crono2250/CL-Feeder_MountingPlate_and_Control/firmware/OpenPnP2_Settings/Actuator_Settings_PostPick.png

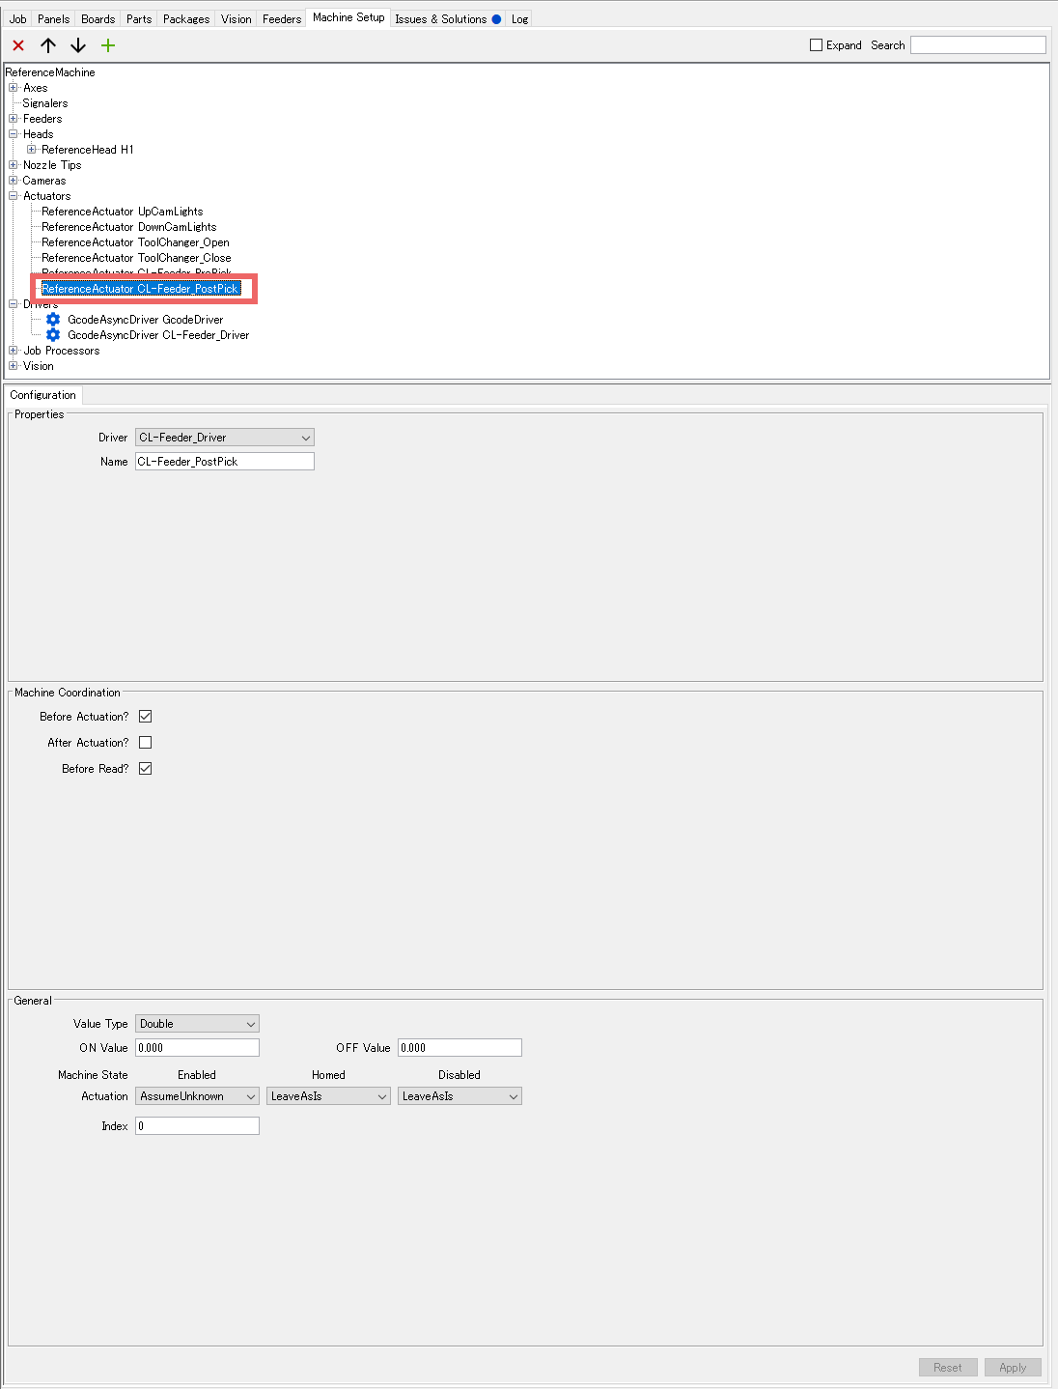
firmware/OpenPnP2_Settings/Actuator_Settings_PostPick.png
