crono2250/CL-Feeder_MountingPlate_and_Control/firmware/OpenPnP2_Settings/GCodeAsyncDriver_Actuator_List.png

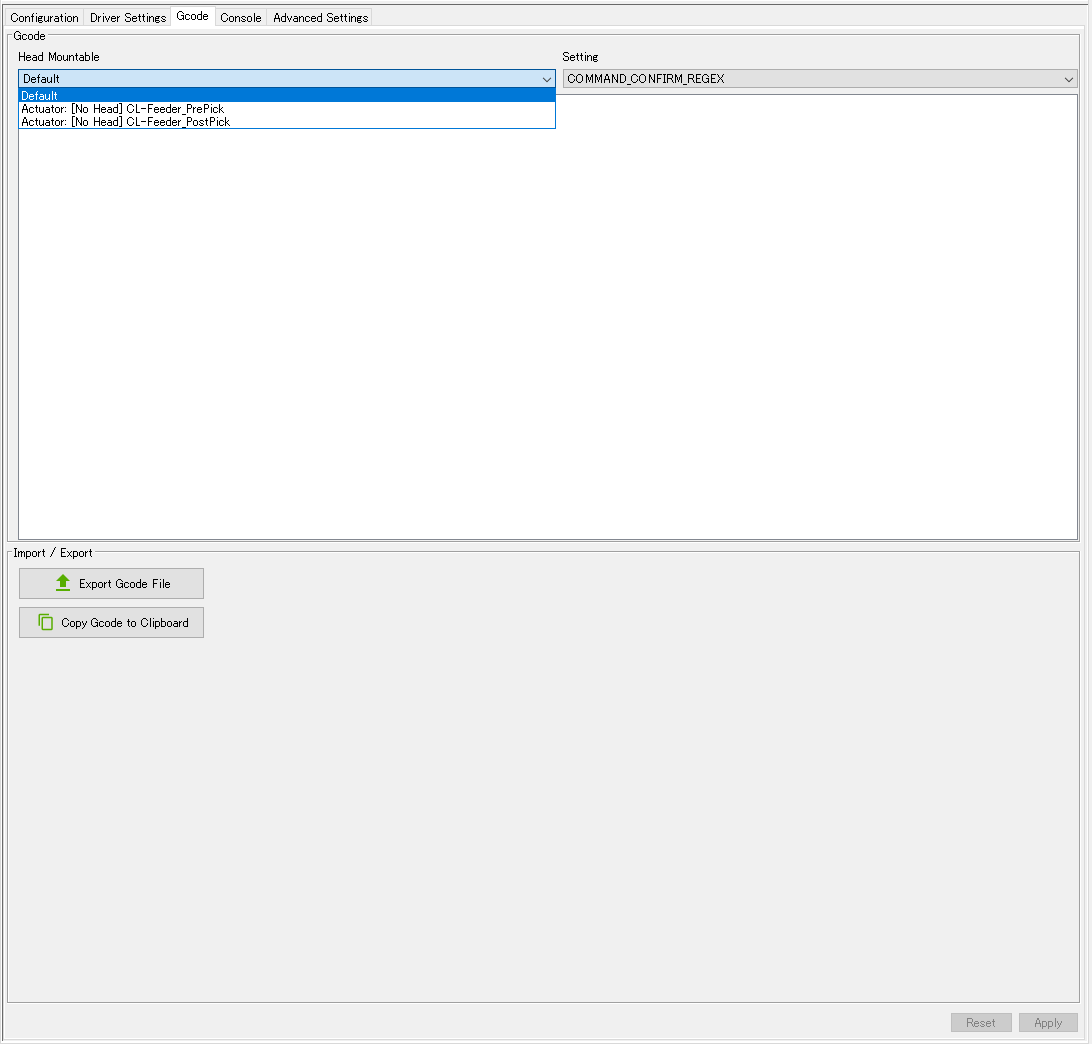
firmware/OpenPnP2_Settings/GCodeAsyncDriver_Actuator_List.png
