crono2250/CL-Feeder_MountingPlate_and_Control/mechanical/img/BuildExample.jpg

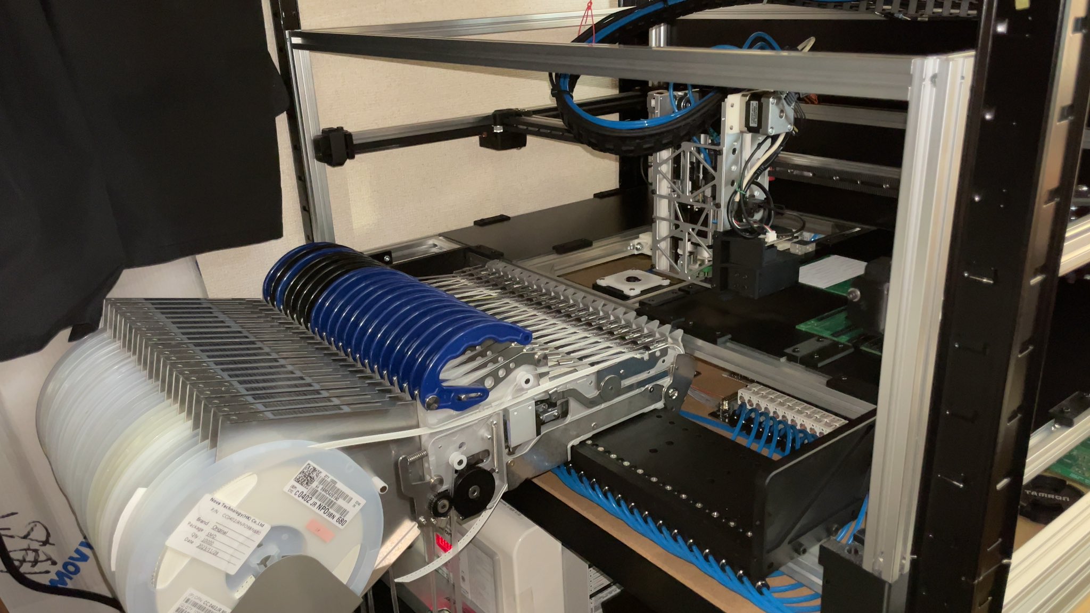
mechanical/img/BuildExample.jpg
