crono2250/CL-Feeder_MountingPlate_and_Control/mechanical/img/BuildExample_CAD.png

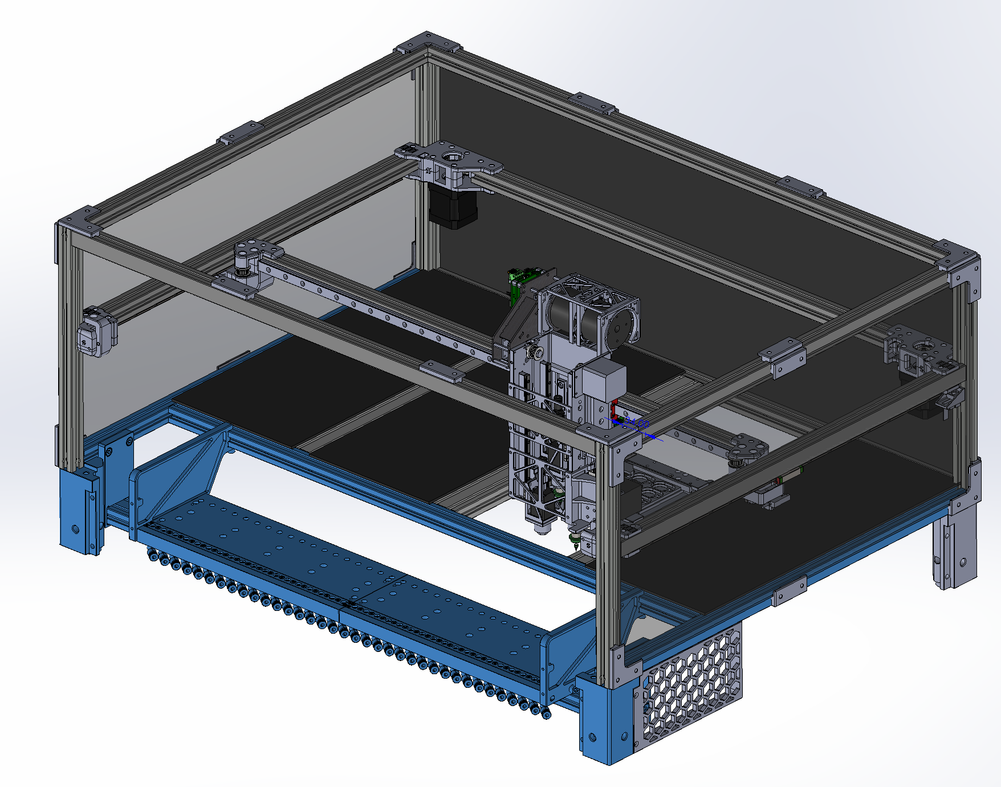
mechanical/img/BuildExample_CAD.png
